danielsaul/phone-tapping-scenario/autocad/plastic_core.bmp

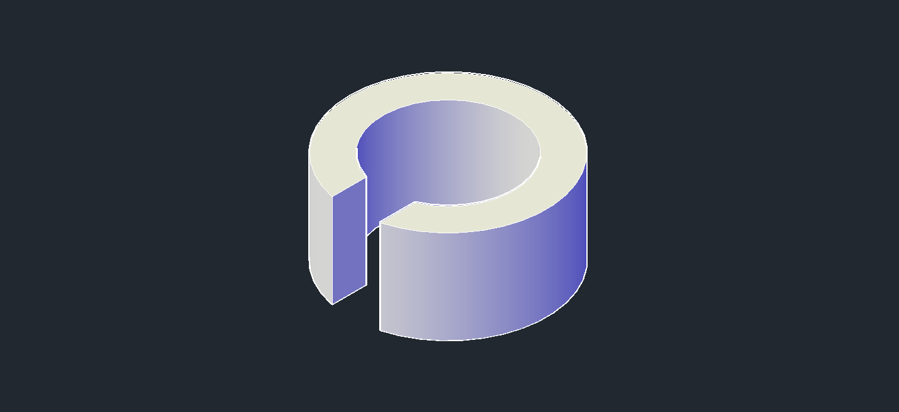
autocad/plastic_core.bmp
