danielsaul/phone-tapping-scenario/img/bandpassfiltercircuit.jpg

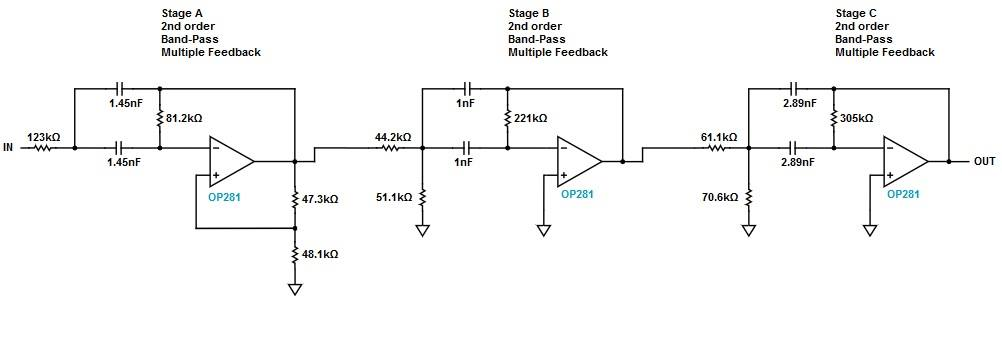
img/bandpassfiltercircuit.jpg
