danielsaul/phone-tapping-scenario/img/multisimbandpasslabelled.jpg

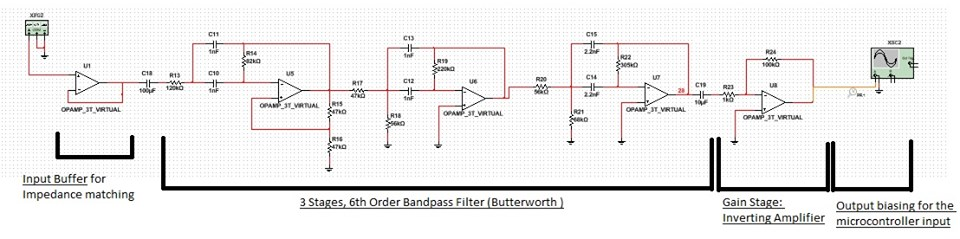
img/multisimbandpasslabelled.jpg
