danielsaul/phone-tapping-scenario/img/newreponsebpfilter.jpg

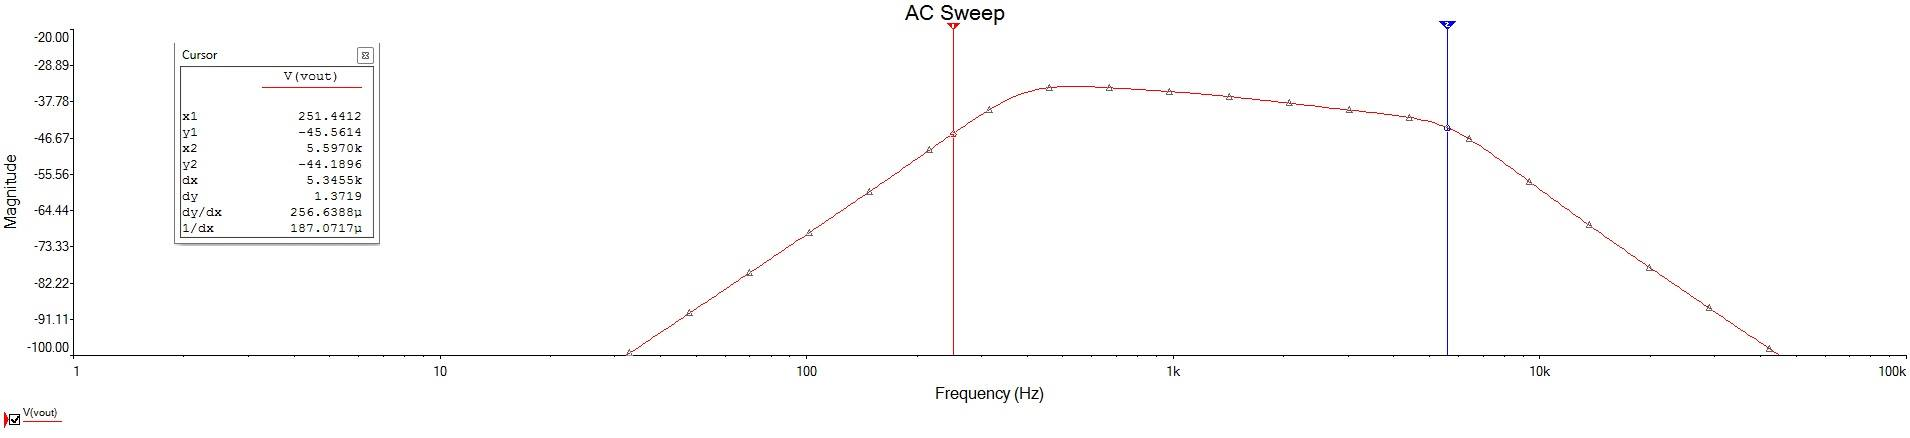
img/newreponsebpfilter.jpg
