danielsaul/phone-tapping-scenario/img/System_diagram.png

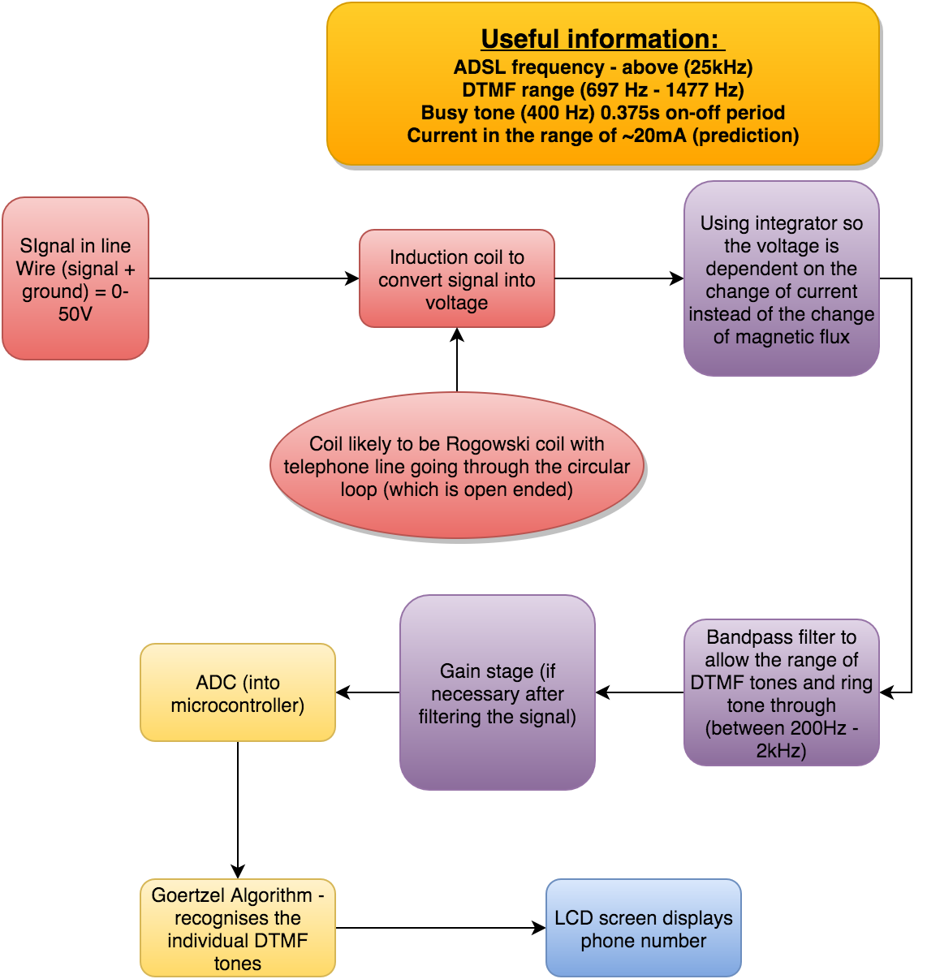
img/System_diagram.png
