danielsaul/phone-tapping-scenario/code/msp430-dtmf-decoder/i2c.h

//
//  i2c.h
//  MSP430RealTimeOS
//
//  Created by Benn Thomsen on 17/10/2014.
//

#ifndef MSP430G2553
#define MSP430G2553
#include <msp430g2553.h>
#endif

void i2cConfigure(void);
void i2cTx(unsigned char address, char *tx_data, unsigned char tx_count);
void i2cRx(unsigned char address, unsigned char rx_count);
